BenRufenacht/KosmoClock/Arduino Code/KosmoBen/LittleBenOutputs.h

#ifndef LITTLEBENOUTPUTS_H
#define LITTLEBENOUTPUTS_H
#include <Arduino.h>

class LittleBenOutput {
  
  private:
   
    void pulseClockDivider();
    void pulseBeat(byte ppqn);
    void pulseRandom();

    byte id;  // ID of the output
    bool outputbit = 1; // 0 or 1 to output 

    byte type; // Clock 0, Beat 1, Random 2

    byte ppqnCount;

    byte clockDividerCount;
    byte clockDivider = 1; 

    byte beatCount;
    byte beatCountDivider = 1;

    byte randomRange = 50;

  public:

    // Functions
    LittleBenOutput(byte id);

    void Pulse(byte ppqn);
    bool GetOutputBit();
    
    String GetName();
    
    String GetTypeName();
    byte GetType();
    String GetTypeValueText(); 
    void SetType(int value);
    void SetTypeValue(int value);

    byte GetclockDivider();
    void SetclockDivider(byte value);
    
    byte GetbeatCountDivider();
    void SetbeatCountDivider(byte value);
    
    byte GetrandomRange();
    void SetrandomRange(byte value);

    void resetCounters(); // Reset all counter used when LittleBen is stopped.
};
#endif
